lbrosnan1/quboElectrical/Thruster Card/Thruster_Control_Card_COPY.kicad_pcb

## KiCad design Thruster Card/Thruster_Control_Card_COPY.kicad_pcb (2025-11-22, an earlier design)

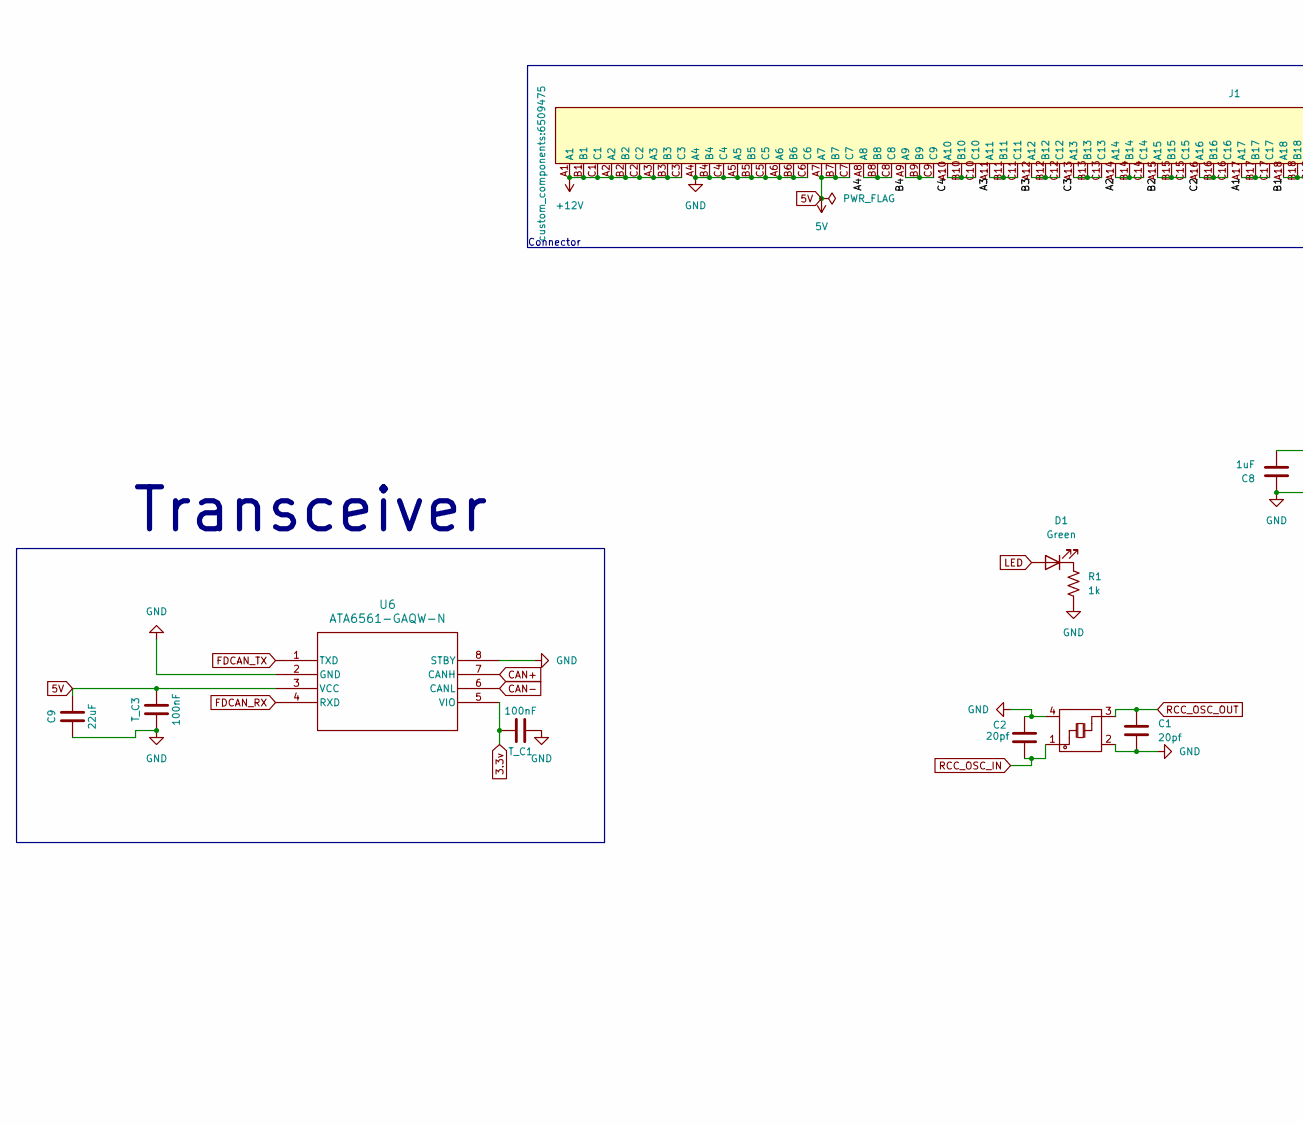
[picture p29: schematic Thruster_Control_Card_COPY.kicad_sch, part in row 1, column 1]

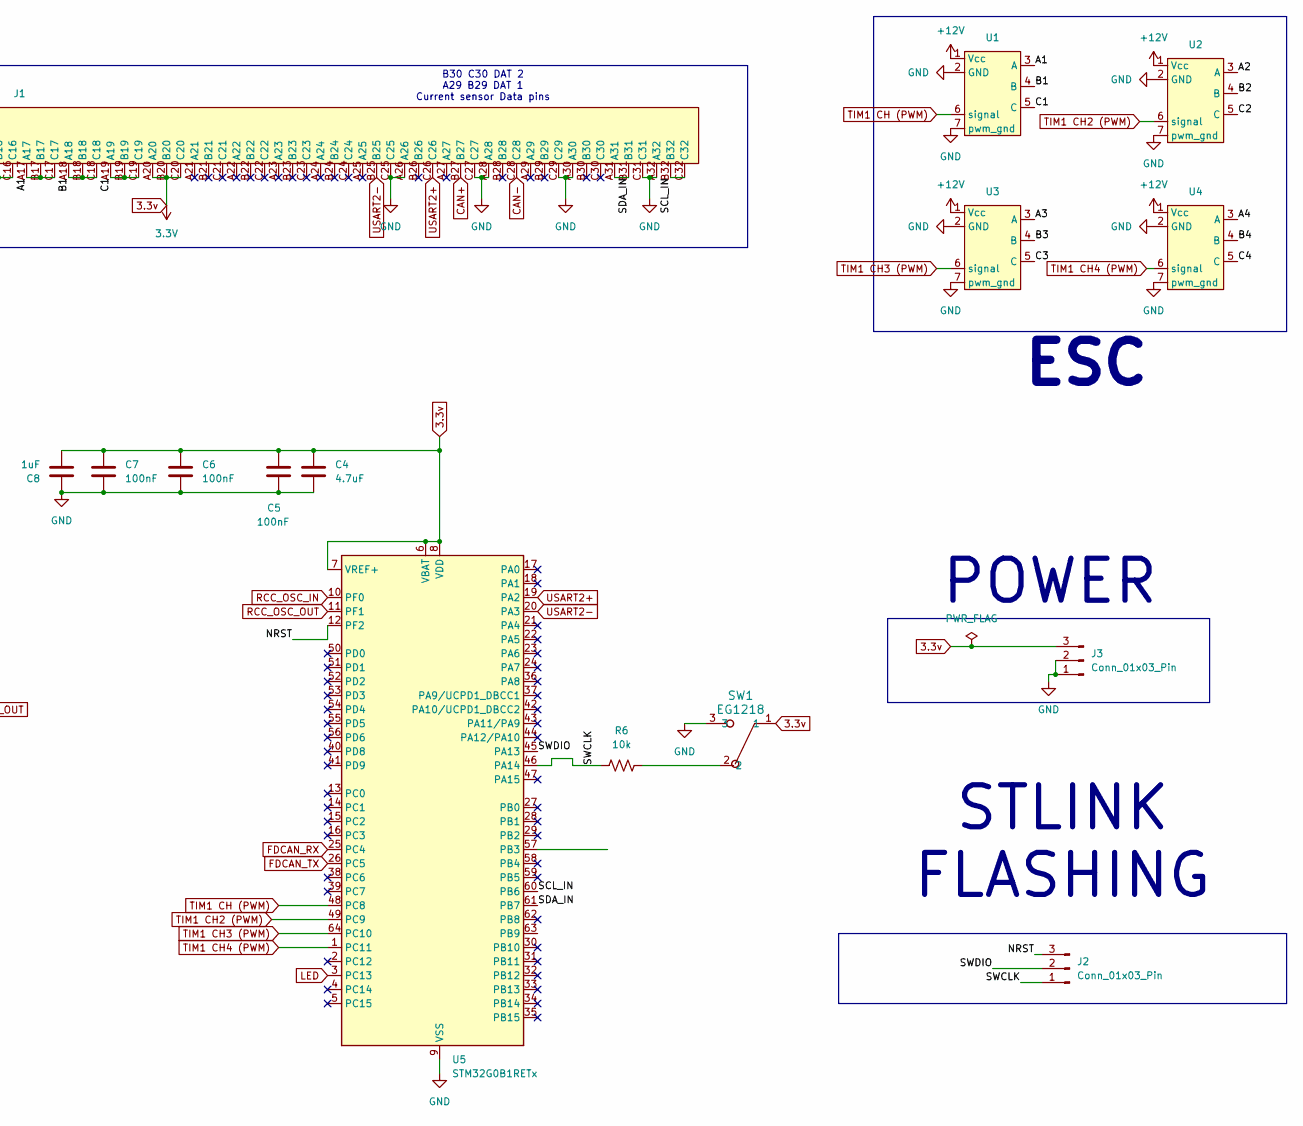
[picture p30: schematic Thruster_Control_Card_COPY.kicad_sch, part in row 1, column 2]

Parts:
C1, C2: 20pf; C_01005_0402Metric
C4: 4.7uF; C_0805_2012Metric_Pad1.18x1.45mm_HandSolder
C5, C6, C7: 100nF; C_0805_2012Metric_Pad1.18x1.45mm_HandSolder
C8: 1uF; C_0805_2012Metric_Pad1.18x1.45mm_HandSolder
C9: 22uF; C_0805_2012Metric_Pad1.18x1.45mm_HandSolder
D1: Green; LED_1206_3216Metric_Pad1.42x1.75mm_HandSolder
J1: 6509475
J2, J3: Conn_01x03_Pin; PinHeader_1x03_P2.54mm_Vertical
R1: 1k; R_1206_3216Metric_Pad1.30x1.75mm_HandSolder
R6: 10k; R_0805_2012Metric_Pad1.20x1.40mm_HandSolder
SW1: EG1218; slide_switch_EGER1218_Thruster
T_C1, T_C3: 100nF; C_0805_2012Metric_Pad1.18x1.45mm_HandSolder
U1, U2, U3, U4: ESC
U5: STM32G0B1RETx; LQFP-64_10x10mm_P0.5mm
U6: ATA6561-GAQW-N; SOIC8_4P9X3P9MC_MCH
U7: YSX321SC_HSE_Oscillator

Connections:
3.3v: C4.1, C5.2, C6.1, C7.1, C8.2, J1.A20, J1.B20, J1.C20, J3.3, SW1.1, T_C1.1, U5.6 (VBAT), U5.7 (VREF+), U5.8 (VDD), U6.5 (VIO)
5V: C9.1, J1.A7, J1.B7, J1.C7, T_C3.1, U6.3 (VCC)
+12V: J1.A1, J1.A2, J1.A3, J1.B1, J1.B2, J1.B3, J1.C1, J1.C2, J1.C3, U1.1 (Vcc), U2.1 (Vcc), U3.1 (Vcc), U4.1 (Vcc)
/A1: J1.A17, J1.B17, J1.C17, U1.3 (A)
/A2: J1.A14, J1.B14, J1.C14, U2.3 (A)
/A3: J1.A11, J1.B11, J1.C11, U3.3 (A)
/A4: J1.A8, J1.B8, J1.C8, U4.3 (A)
/B1: J1.A18, J1.B18, J1.C18, U1.4 (B)
/B2: J1.A15, J1.B15, J1.C15, U2.4 (B)
/B3: J1.A12, J1.B12, J1.C12, U3.4 (B)
/B4: J1.A9, J1.B9, J1.C9, U4.4 (B)
/C1: J1.A19, J1.B19, J1.C19, U1.5 (C)
/C2: J1.A16, J1.B16, J1.C16, U2.5 (C)
/C3: J1.A13, J1.B13, J1.C13, U3.5 (C)
/C4: J1.A10, J1.B10, J1.C10, U4.5 (C)
/NRST: J2.3, U5.12 (PF2)
/SCL_IN: J1.B32, J1.C32, U5.60 (PB6)
/SDA_IN: J1.A31, J1.B31, U5.61 (PB7)
/SWCLK: J2.1, R6.1, U5.46 (PA14)
/SWDIO: J2.2, U5.45 (PA13)
CAN+: J1.B27, U6.7 (CANH)
CAN-: J1.C28, U6.6 (CANL)
FDCAN_RX: U5.25 (PC4), U6.4 (RXD)
FDCAN_TX: U5.26 (PC5), U6.1 (TXD)
GND: C1.1, C2.2, C4.2, C5.1, C6.2, C7.2, C8.1, C9.2, J1.A4, J1.A5, J1.A6, J1.A26, J1.A28, J1.A30, J1.A32, J1.B4, J1.B5, J1.B6, J1.C4, J1.C5, J1.C6, J1.C25, J1.C27, J1.C29, J1.C31, J3.1, J3.2, R1.2, SW1.3, T_C1.2, T_C3.2, U1.2 (GND), U1.7 (pwm_gnd), U2.2 (GND), U2.7 (pwm_gnd), U3.2 (GND), U3.7 (pwm_gnd), U4.2 (GND), U4.7 (pwm_gnd), U5.9 (VSS), U6.2 (GND), U6.8 (STBY), U7.2, U7.4
LED: D1.2 (A), U5.3 (PC13)
unnamed: D1.1 (K), R1.1
unnamed: R6.2, SW1.2
RCC_OSC_IN: C2.1, U5.10 (PF0), U7.1
RCC_OSC_OUT: C1.2, U5.11 (PF1), U7.3
TIM1 CH2 (PWM): U2.6 (signal), U5.49 (PC9)
TIM1 CH3 (PWM): U3.6 (signal), U5.64 (PC10)
TIM1 CH4 (PWM): U4.6 (signal), U5.1 (PC11)
TIM1 CH (PWM): U1.6 (signal), U5.48 (PC8)
USART2+: J1.C26, U5.19 (PA2)
USART2-: J1.B25, U5.20 (PA3)

Notes on the sheet:
B30 C30 DAT 2 A29 B29 DAT 1 Current sensor Data pins
ESC
POWER
Connector
STLINK FLASHING
Transceiver

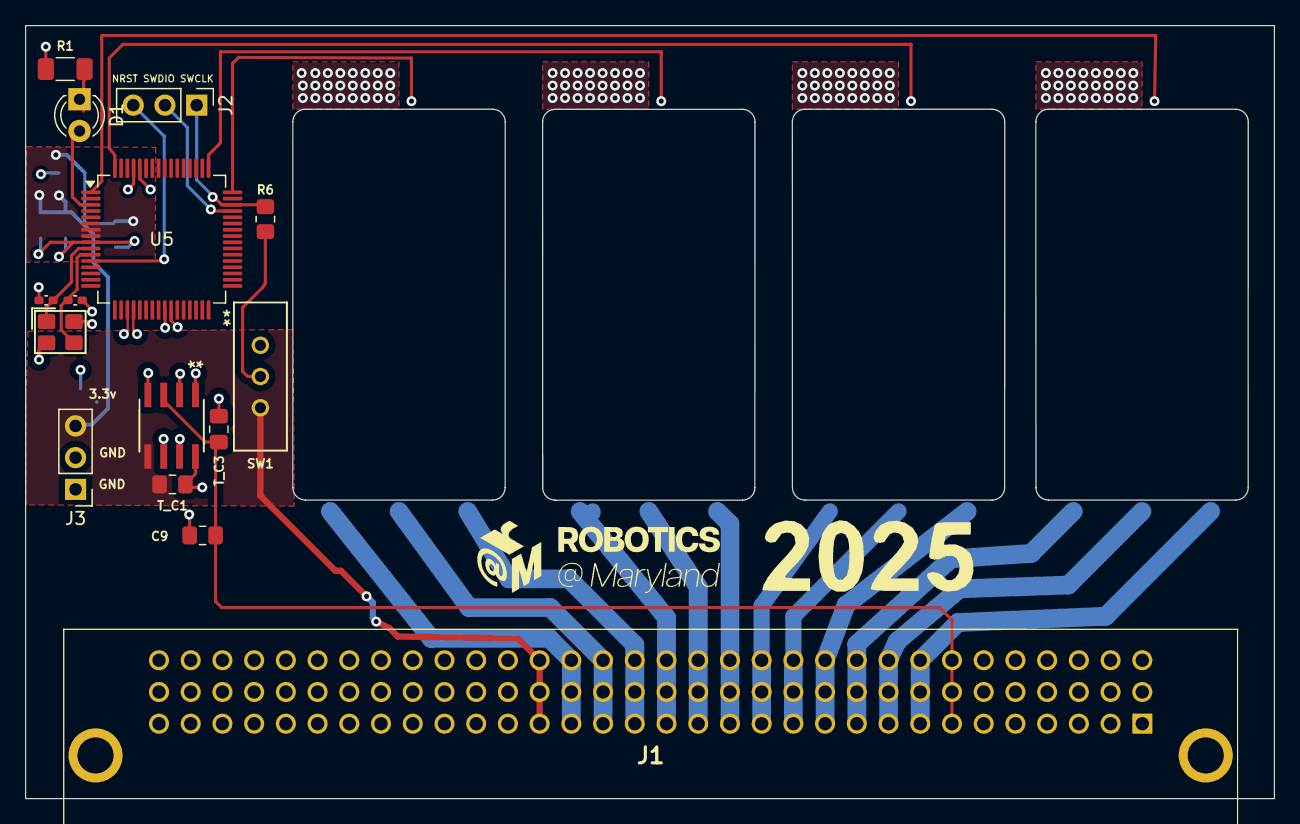
[picture p31: board Thruster_Control_Card_COPY.kicad_pcb from above]

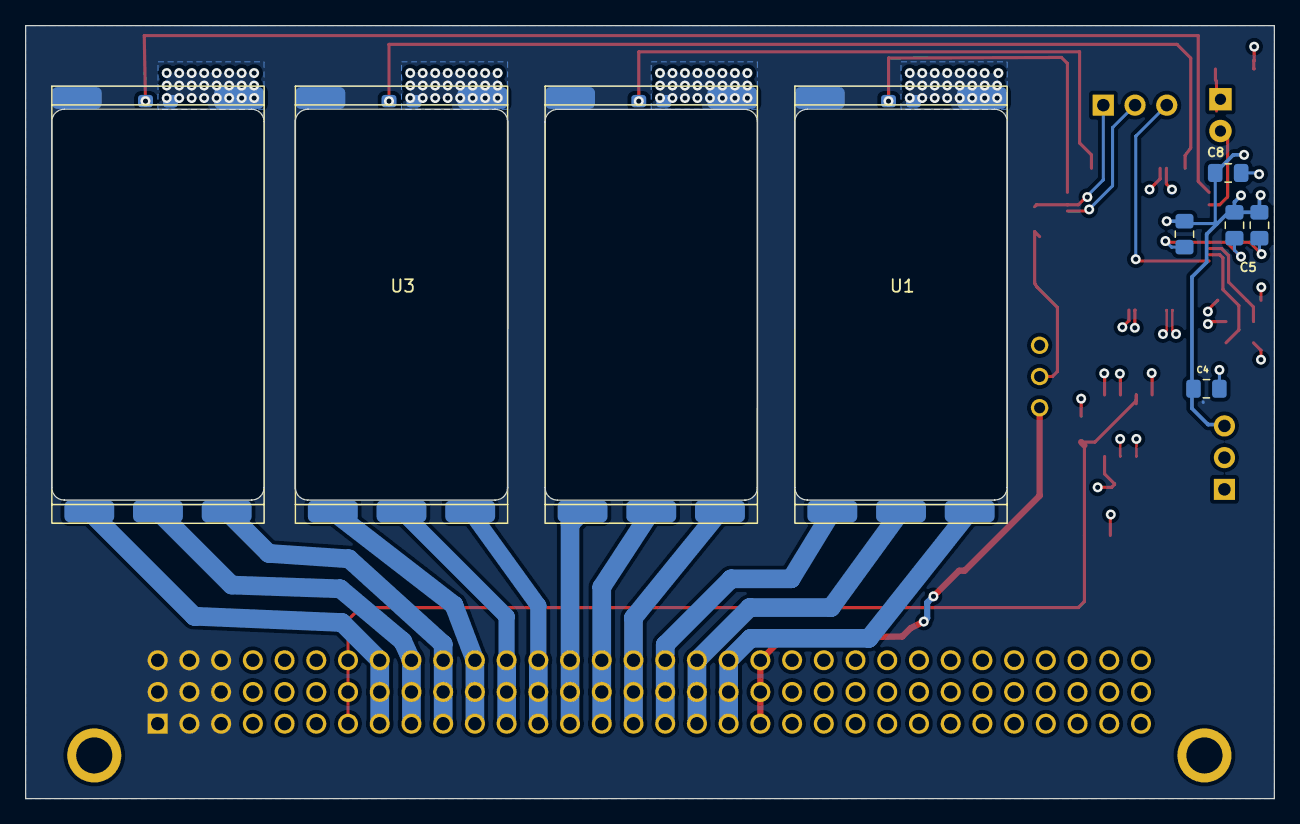
[picture p32: board Thruster_Control_Card_COPY.kicad_pcb from below]

Board: 4 copper layers, 100.0 x 61.9 mm, 24 parts (9 on the bottom side), 36 nets.
