lbrosnan1/quboElectrical/Thruster Card/Cards/Power_Control_Card/Power_Control_Card.kicad_pcb

## KiCad design Thruster Card/Cards/Power_Control_Card/Power_Control_Card.kicad_pcb (2025-11-22)

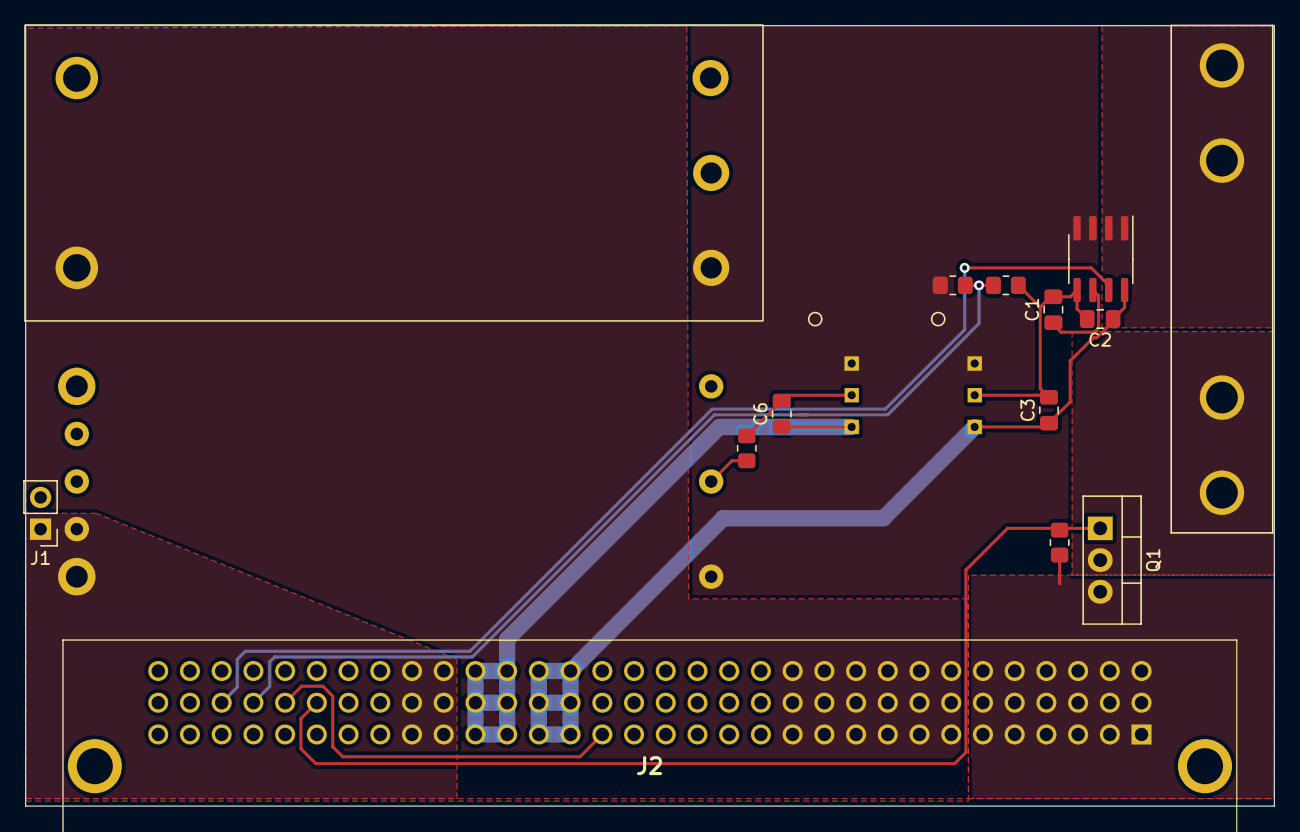
[picture p33: board Power_Control_Card.kicad_pcb from above]

Board: 2 copper layers, 100.0 x 62.5 mm, 17 parts (1 on the bottom side), 14 nets.

Parts:
20A1: Fuse; 1.25__FUSECLIPS
C1: 47n; C_0805_2012Metric_Pad1.18x1.45mm_HandSolder
C2: 0.1u; C_0805_2012Metric_Pad1.18x1.45mm_HandSolder
C3, C6: 1u; C_0805_2012Metric_Pad1.18x1.45mm_HandSolder
DC/DC_CNVRT1: TSR2-2450; TSR2
DC/DC_CNVRT2: TSR2-2433; TSR2
INPT_CRRNT_SNSR1: TMCS1101A4B; SOIC-8_3.9x4.9mm_P1.27mm
J1: Conn_01x02; PinHeader_1x02_P2.54mm_Vertical
J2: 6509475
Q1: FQPF27P06; TO-220-3_Vertical
RSW1, RSW2: 10kO; R_0805_2012Metric_Pad1.20x1.40mm_HandSolder
U1: 240W_CONV
U2: 72W_CONV
VDIV1(R)1: 90kO; R_0805_2012Metric_Pad1.20x1.40mm_HandSolder
VDIV2(R)1: 10kO; R_0805_2012Metric_Pad1.20x1.40mm_HandSolder

Connections:
12V_Jetson: J1.1, J2.A23, J2.A24, J2.B23, J2.B24, J2.C23, J2.C24, U2.7 (SENSE+), U2.8 (VOUT)
+3.3V: C6.1, DC/DC_CNVRT2.3 (+V_OUT), J2.A21, J2.A22, J2.B21, J2.B22, J2.C21, J2.C22
+5V: C2.1, C3.1, DC/DC_CNVRT1.3 (+V_OUT), INPT_CRRNT_SNSR1.8 (VCC), J2.A19, J2.A20, J2.B19, J2.B20, J2.C19, J2.C20
+12V: J2.A7, J2.A8, J2.A9, J2.A10, J2.A11, J2.A12, J2.B7, J2.B8, J2.B9, J2.B10, J2.B11, J2.B12, J2.C7, J2.C8, J2.C9, J2.C10, J2.C11, J2.C12, U1.8 (VOUT)
+24V: J2.A1, J2.A2, J2.A3, J2.A4, J2.A5, J2.A6, J2.B1, J2.B2, J2.B3, J2.B4, J2.B5, J2.B6, J2.C1, J2.C2, J2.C3, J2.C4, J2.C5, J2.C6, Q1.3 (S), RSW1.1
/VBATT: 20A1.P$2 (4), INPT_CRRNT_SNSR1.1 (IP+)
/V_POWER: DC/DC_CNVRT1.1 (+V_IN), DC/DC_CNVRT2.1 (+V_IN), INPT_CRRNT_SNSR1.3 (IP-), U1.1 (VIN), U2.1 (VIN), VDIV1(R)1.1
DAT1: J2.B29, VDIV1(R)1.2, VDIV2(R)1.1
DAT2: INPT_CRRNT_SNSR1.7 (VIOUT), J2.B30
unnamed: 20A1.P$1 (1), Q1.2 (D)
unnamed: C1.1, INPT_CRRNT_SNSR1.6 (FILTER)
unnamed: RSW2.1, U2.2 (ON/OFF)
SW1: C1.2, C2.2, C3.2, C6.2, DC/DC_CNVRT1.2 (GND), DC/DC_CNVRT2.2 (GND), INPT_CRRNT_SNSR1.5 (GND), J1.2, J2.A13, J2.A14, J2.A15, J2.A16, J2.A17, J2.A18, J2.B13, J2.B14, J2.B15, J2.B16, J2.B17, J2.B18, J2.B28, J2.C13, J2.C14, J2.C15, J2.C16, J2.C17, J2.C18, RSW2.2, U1.3 (IN-), U1.4 (OUT-), U2.3 (IN-), U2.4 (OUT-), U2.5 (SENSE-), VDIV2(R)1.2
SW2: J2.B27, Q1.1 (G), RSW1.2
